smarthomefans/z2m_partner/images/flash/info.png

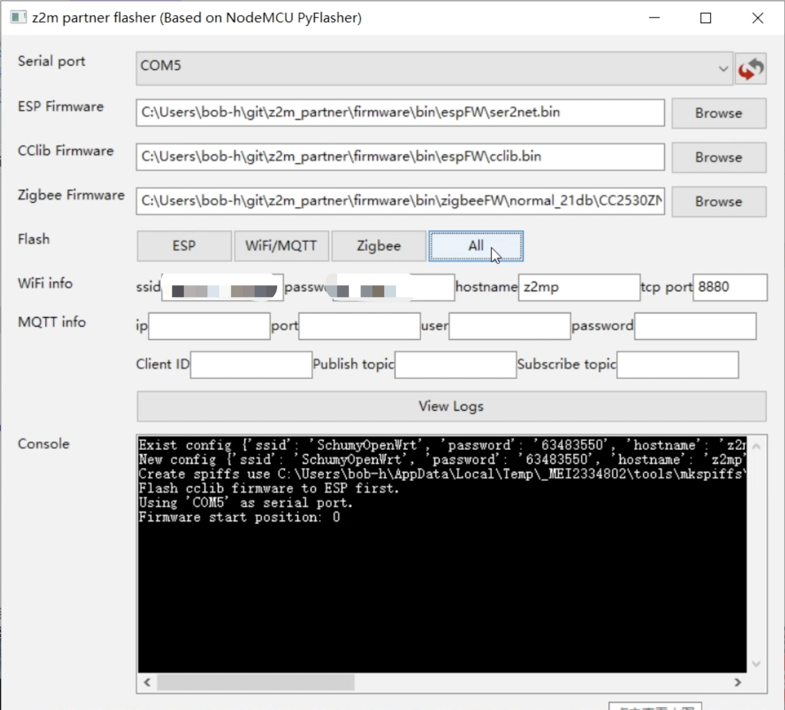
images/flash/info.png
