smarthomefans/z2m_partner/images/tasmota/console1.jpg

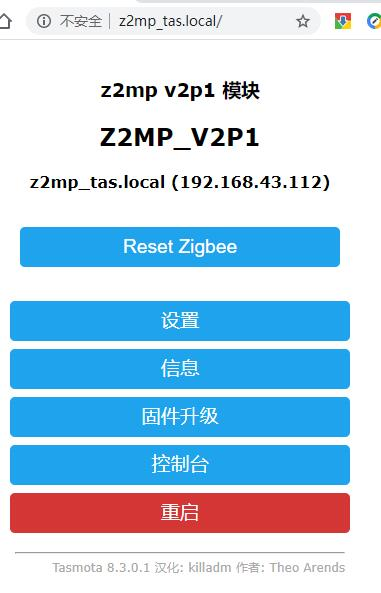
images/tasmota/console1.jpg
