smarthomefans/z2m_partner/images/tasmota/updata_zigbee_c.jpg

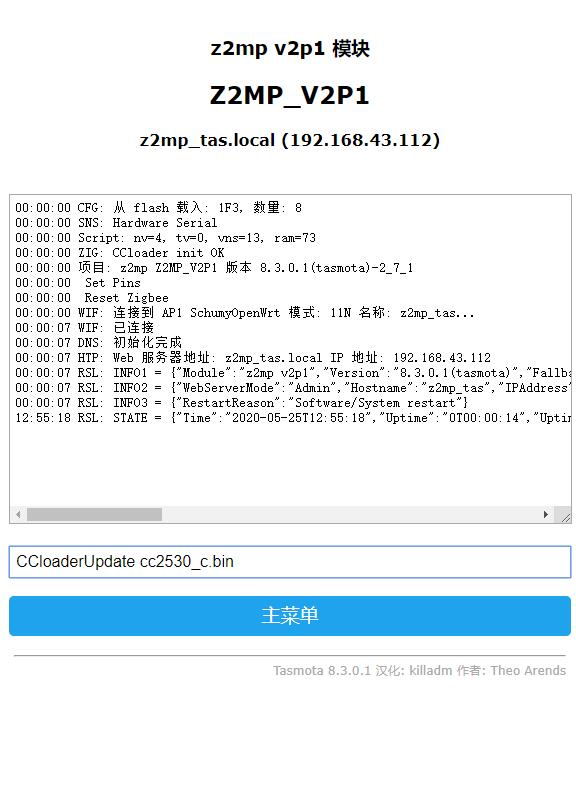
images/tasmota/updata_zigbee_c.jpg
