smarthomefans/z2m_partner/firmware/esp/cclib/CCDebugger.h

/**
 *
 * CC-Debugger Protocol Library for Arduino
 * Copyright (c) 2014 Ioannis Charalampidis
 * Copyright (c) 2015 Simon Schulz - github.com/fishpepper
 *
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
 * You should have received a copy of the GNU General Public License
 * along with this program.  If not, see <http://www.gnu.org/licenses/>.
 */

#ifndef CCDEBUGGER_H
#define CCDEBUGGER_H

#define CC_ERROR_NONE           0
#define CC_ERROR_NOT_ACTIVE     1
#define CC_ERROR_NOT_DEBUGGING  2
#define CC_ERROR_NOT_WIRED      3

// For arduino bindings
#include "Arduino.h"

class CCDebugger {
public:

  ////////////////////////////
  // Configuration
  ////////////////////////////

  /**
   * Initialize CC Debugger class
   */
  CCDebugger( int pinRST, int pinDC, int pinDD);

  /**
   * Activate/deactivate debugger
   */
  void setActive( boolean on );

  /**
   * Return the error flag
   */
  byte error();

  ////////////////////////////
  // High-Level interaction
  ////////////////////////////

  /**
   * Enter debug mode
   */
  byte enter();

  /**
   * Exit from debug mode
   */
  byte exit();

  /**
   * Execute a CPU instructuion
   */
  byte exec( byte oc0 );
  byte exec( byte oc0, byte oc1 );
  byte exec( byte oc0, byte oc1, byte oc2 );
  byte execi( byte oc0, unsigned short c0 );

  /**
   * Return chip ID
   */
  unsigned short getChipID();

  /**
   * Return PC
   */
  unsigned short getPC();

  /**
   * Return debug status
   */
  byte getStatus();

   /**
   * resume program exec
   */
  byte resume();

  /**
   * halt program exec
   */
  byte halt();

  /**
   * Step a single instruction
   */
  byte step();

  /**
   * Get debug configuration
   */
  byte getConfig();

  /**
   * Set debug configuration
   */
  byte setConfig( byte config );

  /**
   * Massive erasure on the chip
   */
  byte chipErase();

  ////////////////////////////
  // Low-level interaction
  ////////////////////////////

  /**
   * Write to the debugger
   */
  byte write( byte data );

  /**
   * Wait until we are ready to read & Switch to read mode
   */
  byte switchRead( byte maxWaitCycles = 255 );

  /**
   * Switch to write mode
   */
  byte switchWrite();

  /**
   * Read from the debugger
   */
  byte read();

  /**
   * Update the debug instruction table
   */
  byte updateInstructionTable( byte newTable[16] );

  /**
   * Get the instruction table version
   */
  byte getInstructionTableVersion();


private:

  ////////////////////////////
  // Private/Helper parts
  ////////////////////////////

  /**
   * Switch reset pin
   */
  void setDDDirection( byte direction );

  /**
   * Software-overridable instruction table that can be used
   * for supporting other CCDebug-Compatible chips purely by software
   */
  byte      instr[16];

  /**
   * Local properties
   */
  int       pinRST;
  int       pinDC;
  int       pinDD;
  byte      errorFlag;
  byte      ddIsOutput;
  byte      inDebugMode;
  boolean   active;

};

#endif
